SamihaHassan/Robot_Arm/Robot_Arm_PIO/include/globals.h

#ifndef GLOBAL_H
#define GLOBAL_H

#define CONST_NUM 3

//Pin assignments
#define RUPT_PIN_A 2
#define RUPT_PIN_B 3
#define MOTOR_PIN_A 4
#define DIREC_A 7
#define DIREC_B 6

#define DEG(A) ( ((A) < 0) ? 360 + (A) : (A) )


#endif
